harsh-gupta-10/macropad3x3oled/software/components/profiles_section.py

import tkinter as tk
from engine import load_profiles, load_settings

class ProfilesSection:
    def __init__(self, root, app=None):
        self.root = root
        self.app = app  # Reference to main app
        
        profile_frame = tk.Frame(self.root, bg="#0F172A", bd=1, relief="ridge", highlightbackground="#1E293B", highlightthickness=1)
        profile_frame.place(x=10, y=10, width=180, height=430)

        tk.Label(profile_frame, text="Profiles", bg="#0F172A", fg="#E2E8F0", font=("Segoe UI", 13, "bold"), pady=10).pack()
        
        self.profile_buttons = []
        profiles = load_profiles()
        settings = load_settings()
        active_profiles = settings.get("active_profiles", 6)
        
        profile_names = {
            "0": "Default", 
            "1": "VSCode", 
            "2": "OBS", 
            "3": "Software", 
            "4": "Windows", 
            "5": "Photoshop",
            "6": "Profile 7",
            "7": "Profile 8",
            "8": "Profile 9",
            "9": "Profile 10"
        }
        
        # Only create buttons for active profiles
        for i in range(active_profiles):
            profile_id = str(i)
            name = profile_names.get(profile_id, f"Profile {i + 1}")
            btn = tk.Button(profile_frame, text=name, bg="#1E293B", fg="#E2E8F0", relief="flat",
                            font=("Segoe UI", 10, "bold"), activebackground="#0EA5E9", activeforeground="#082F49",
                            command=lambda p=profile_id: self.select_profile(p))
            btn.pack(fill="x", padx=6, pady=4, ipady=3)
            self.profile_buttons.append((profile_id, btn))

    def select_profile(self, profile):
        """Handle profile selection."""
        # Update button appearance
        for profile_id, btn in self.profile_buttons:
            if profile_id == profile:
                btn.config(bg="#0EA5E9", fg="#082F49")
            else:
                btn.config(bg="#1E293B", fg="#E2E8F0")
                
        # Update the app's selected profile
        if self.app:
            self.app.set_selected_profile(profile)
